nic6911/HPACS/Software/HMI/auto3.png

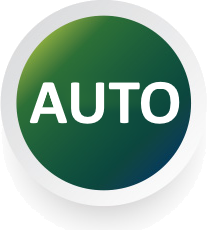
Software/HMI/auto3.png
