nic6911/HPACS/Software/HMI/auto2.png

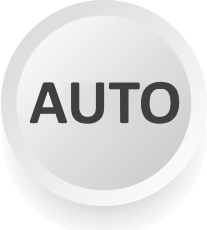
Software/HMI/auto2.png
