nic6911/HPACS/Software/HMI/hot_warning.png

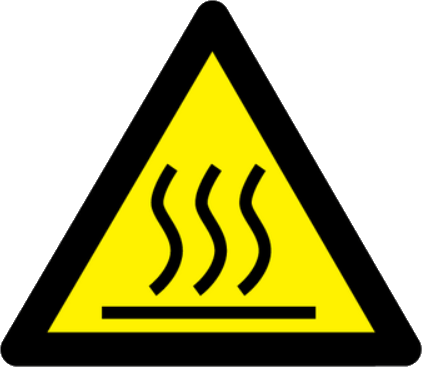
Software/HMI/hot_warning.png
