nic6911/HPACS/Software/HMI/hotplate.png

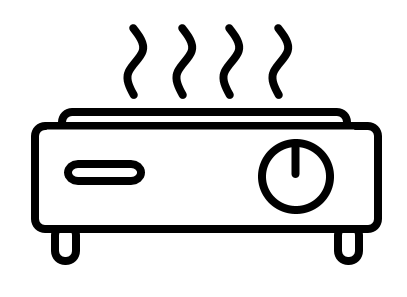
Software/HMI/hotplate.png
