nic6911/HPACS/Software/HMI/off.png

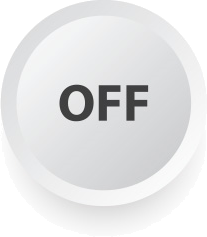
Software/HMI/off.png
