nic6911/HPACS/Software/HMI/offred.png

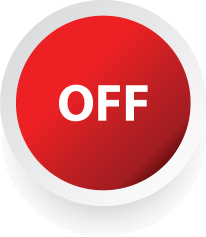
Software/HMI/offred.png
