nic6911/HPACS/Software/HMI/on.png

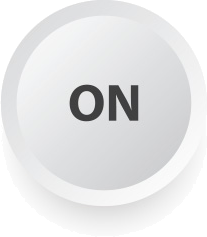
Software/HMI/on.png
