nic6911/HPACS/Software/HMI/ongreen.png

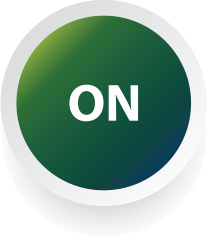
Software/HMI/ongreen.png
