nic6911/HPACS/Software/HMI/save1.png

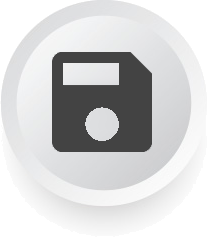
Software/HMI/save1.png
