nic6911/HPACS/Software/HMI/save2.png

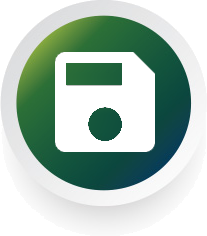
Software/HMI/save2.png
